HackerSchool/hswatch/Android/hswatch_connection_module/src/main/ic_launcher-playstore.png

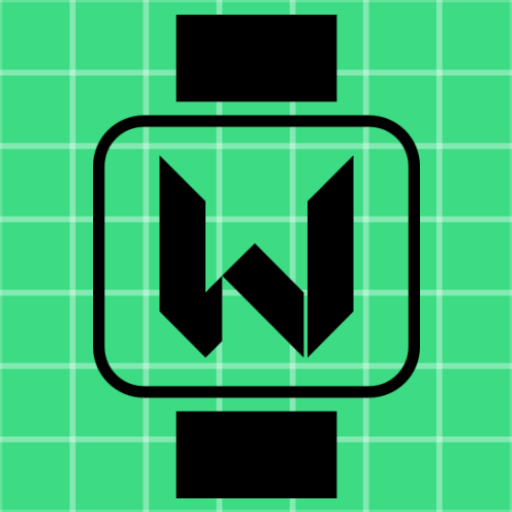
Android/hswatch_connection_module/src/main/ic_launcher-playstore.png
