HackerSchool/hswatch/docs/img/HSWatch_front.jpg

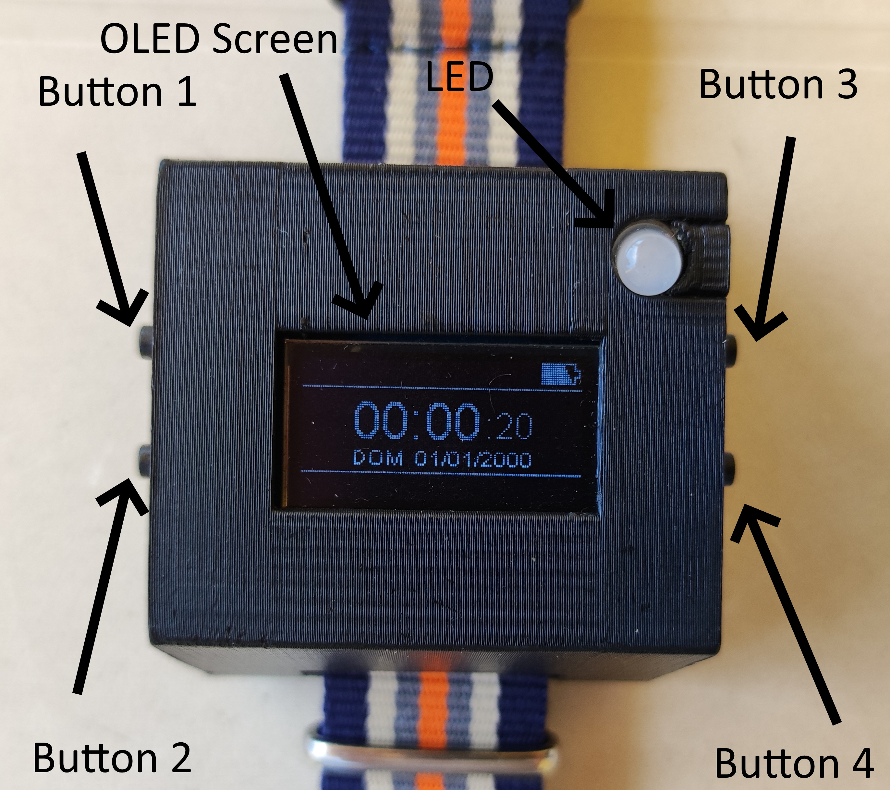
docs/img/HSWatch_front.jpg
