HackerSchool/hswatch/docs/img/HSWatch_side.jpg

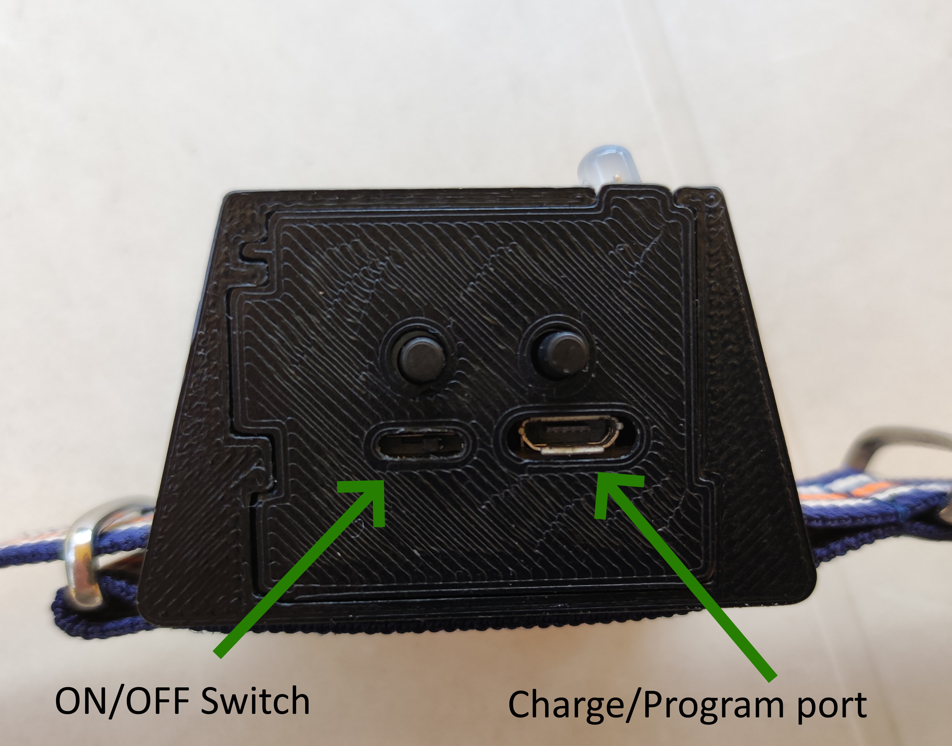
docs/img/HSWatch_side.jpg
