HackerSchool/hswatch/docs/img/pcb_back.png

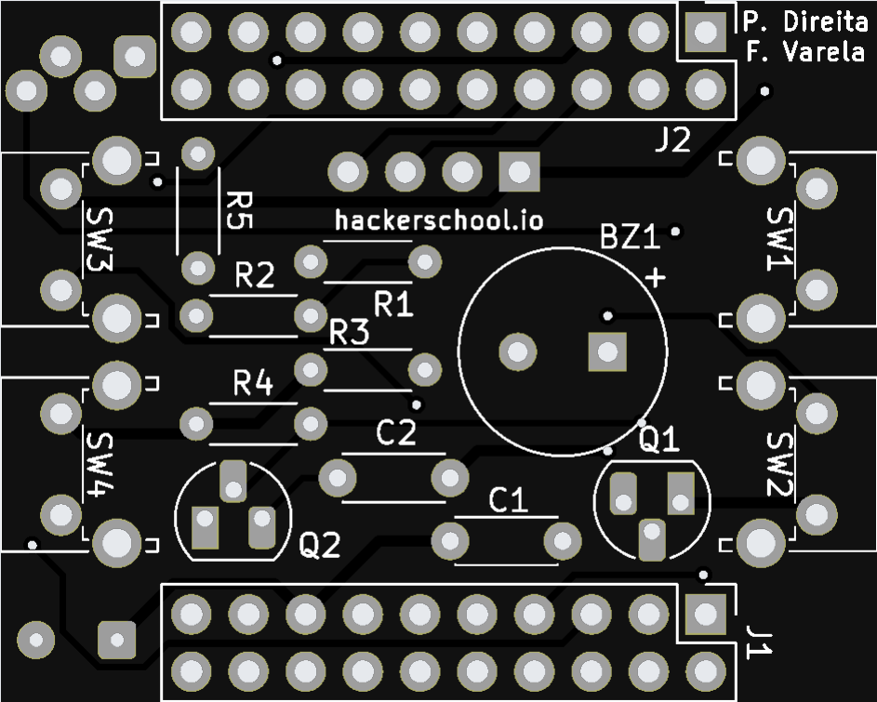
docs/img/pcb_back.png
