HackerSchool/hswatch/docs/img/pcb_front.png

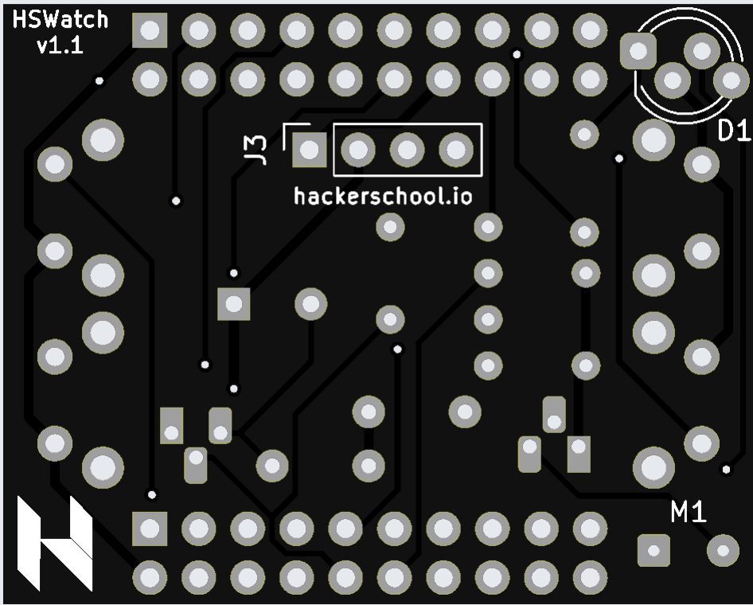
docs/img/pcb_front.png
