HackerSchool/hswatch/docs/img/peripheral_board_back.jpg

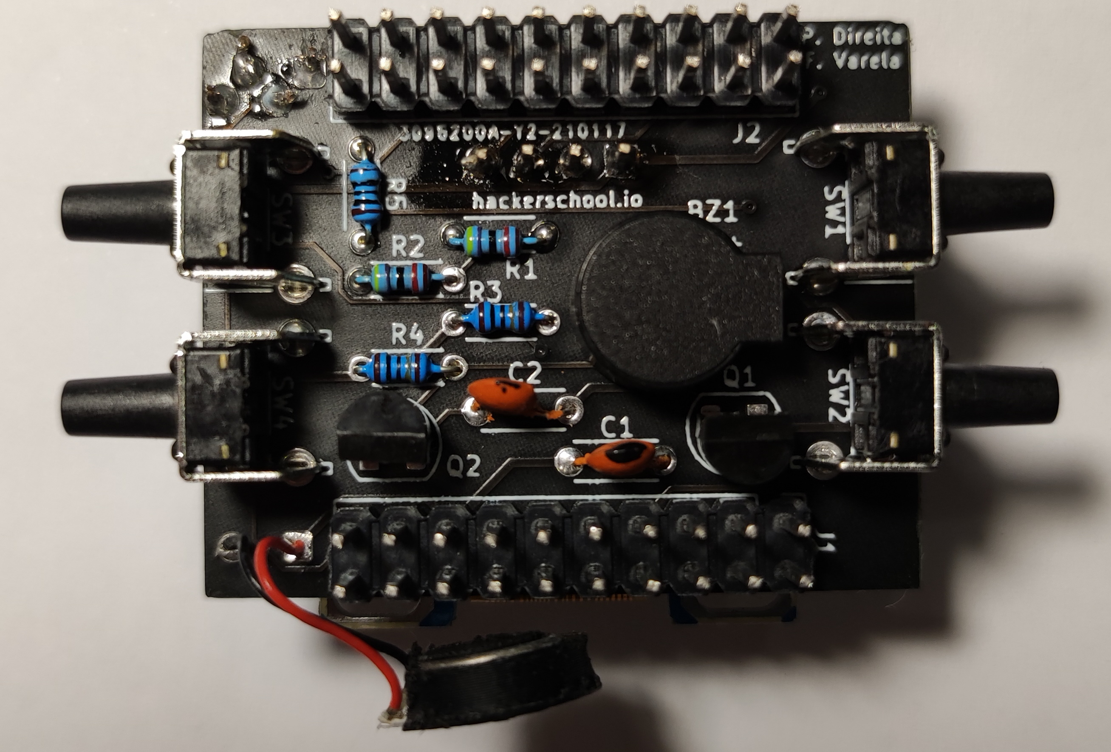
docs/img/peripheral_board_back.jpg
