HackerSchool/hswatch/docs/img/peripheral_board_front.jpg

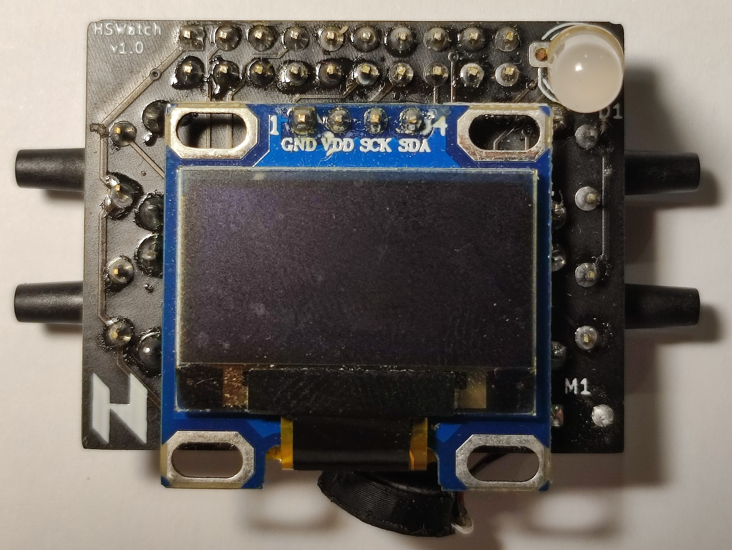
docs/img/peripheral_board_front.jpg
