HackerSchool/hswatch/docs/img/upload.png

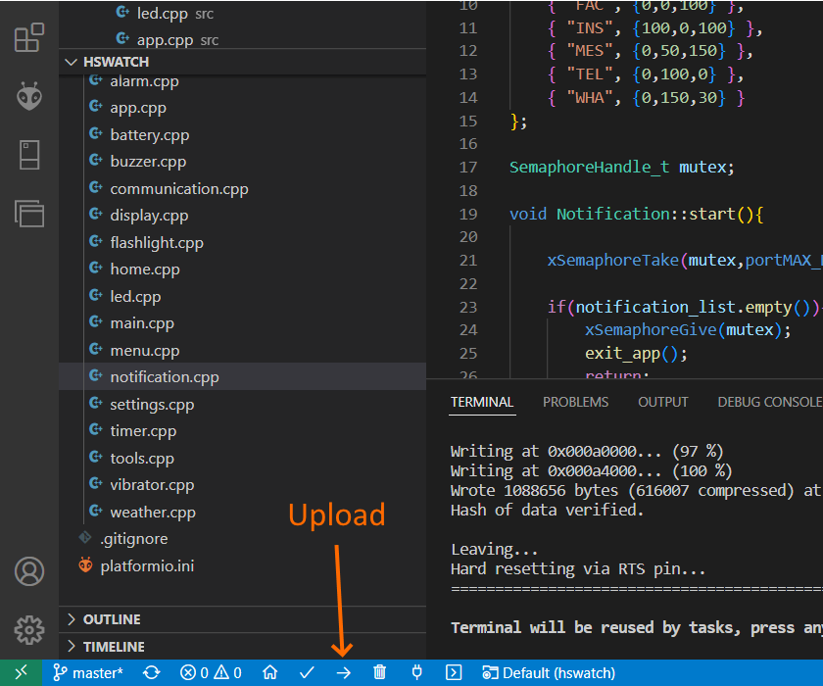
docs/img/upload.png
