HackerSchool/hswatch/docs/img/components/2N-700.jpg

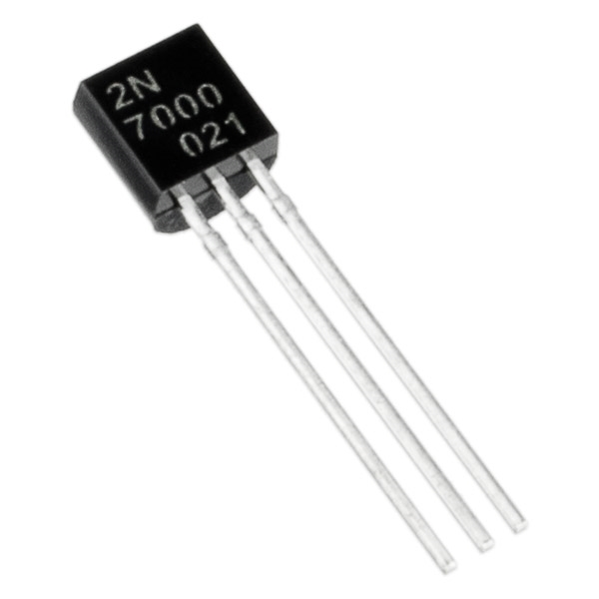
docs/img/components/2N-700.jpg
