HackerSchool/hswatch/docs/img/components/oled.png

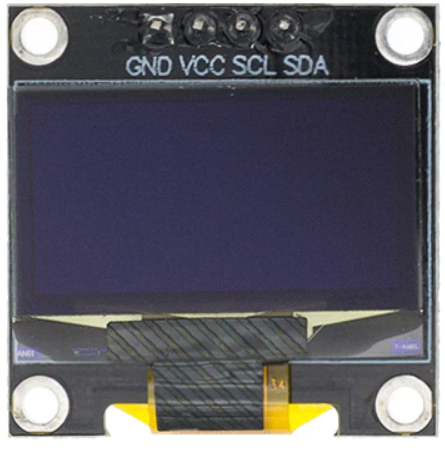
docs/img/components/oled.png
