HackerSchool/hswatch/docs/img/components/pin_header.jpg

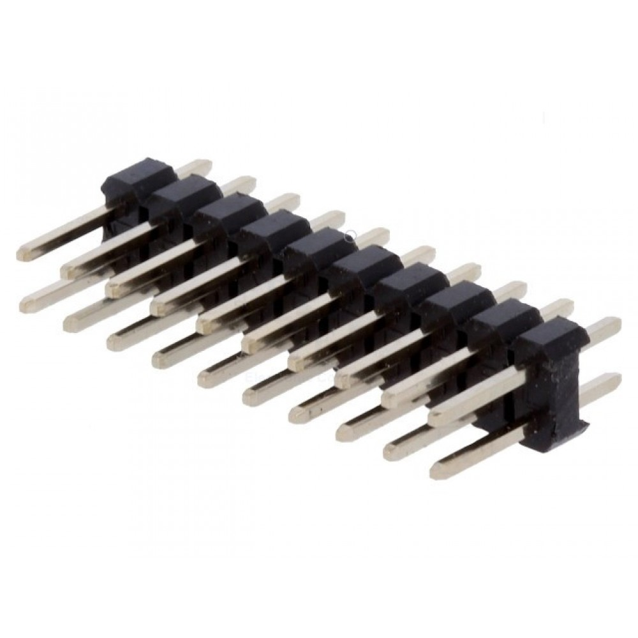
docs/img/components/pin_header.jpg
