HackerSchool/hswatch/docs/img/components/ttgo.png

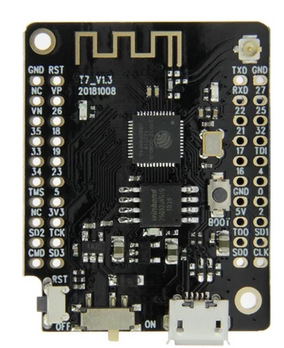
docs/img/components/ttgo.png
