HackerSchool/hswatch/docs/img/platformio-install.png

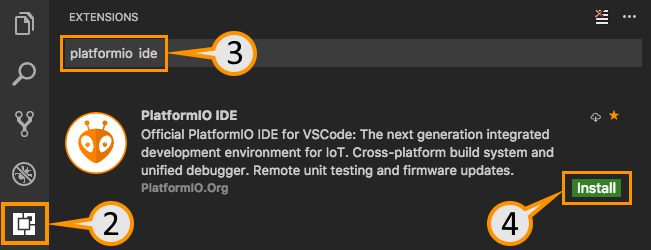
docs/img/platformio-install.png
