HackerSchool/hswatch/docs/img/soldering_tips.jpg

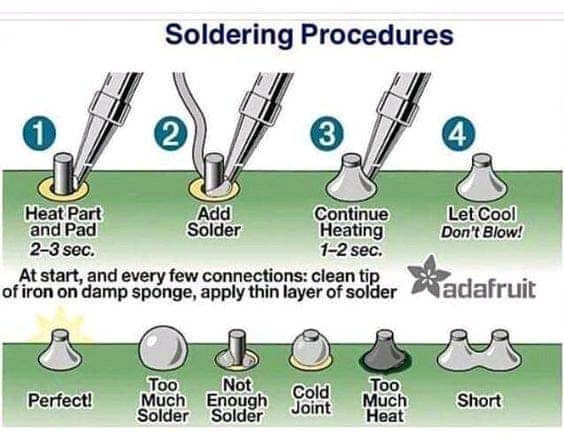
docs/img/soldering_tips.jpg
