HackerSchool/hswatch/docs/img/user_manual/alarm.png

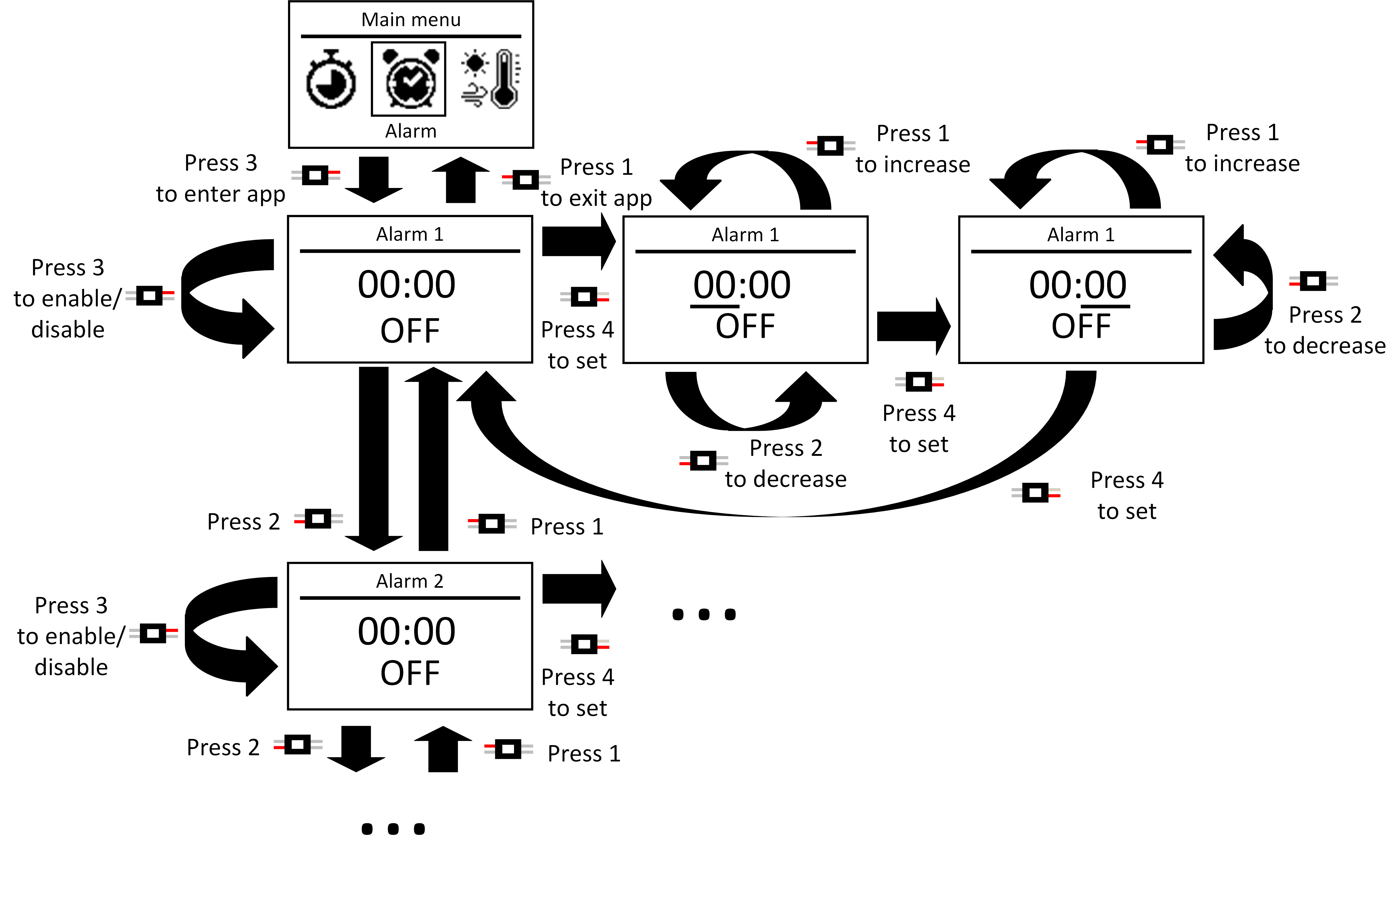
docs/img/user_manual/alarm.png
