HackerSchool/hswatch/docs/img/user_manual/chronograph_timer.png

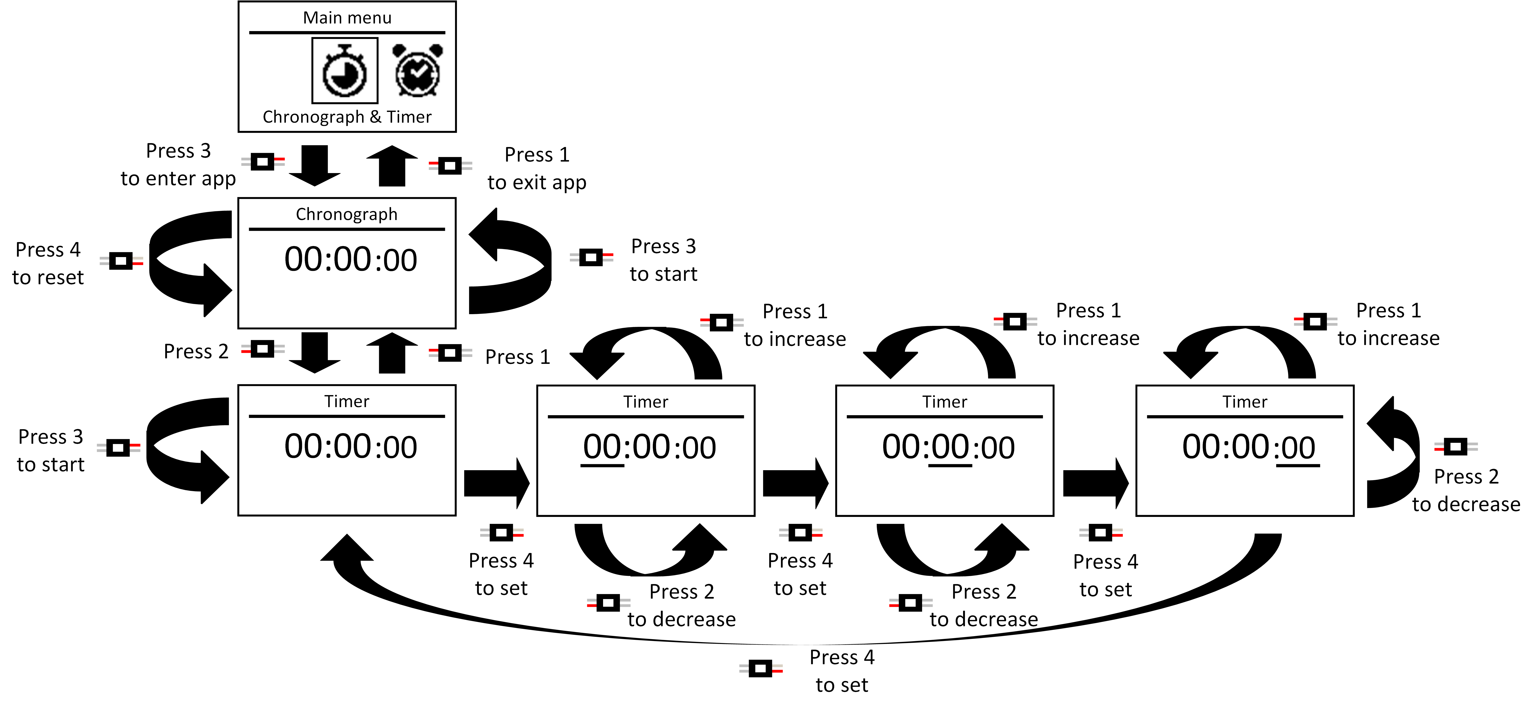
docs/img/user_manual/chronograph_timer.png
