HackerSchool/hswatch/docs/img/user_manual/clock_menu.png

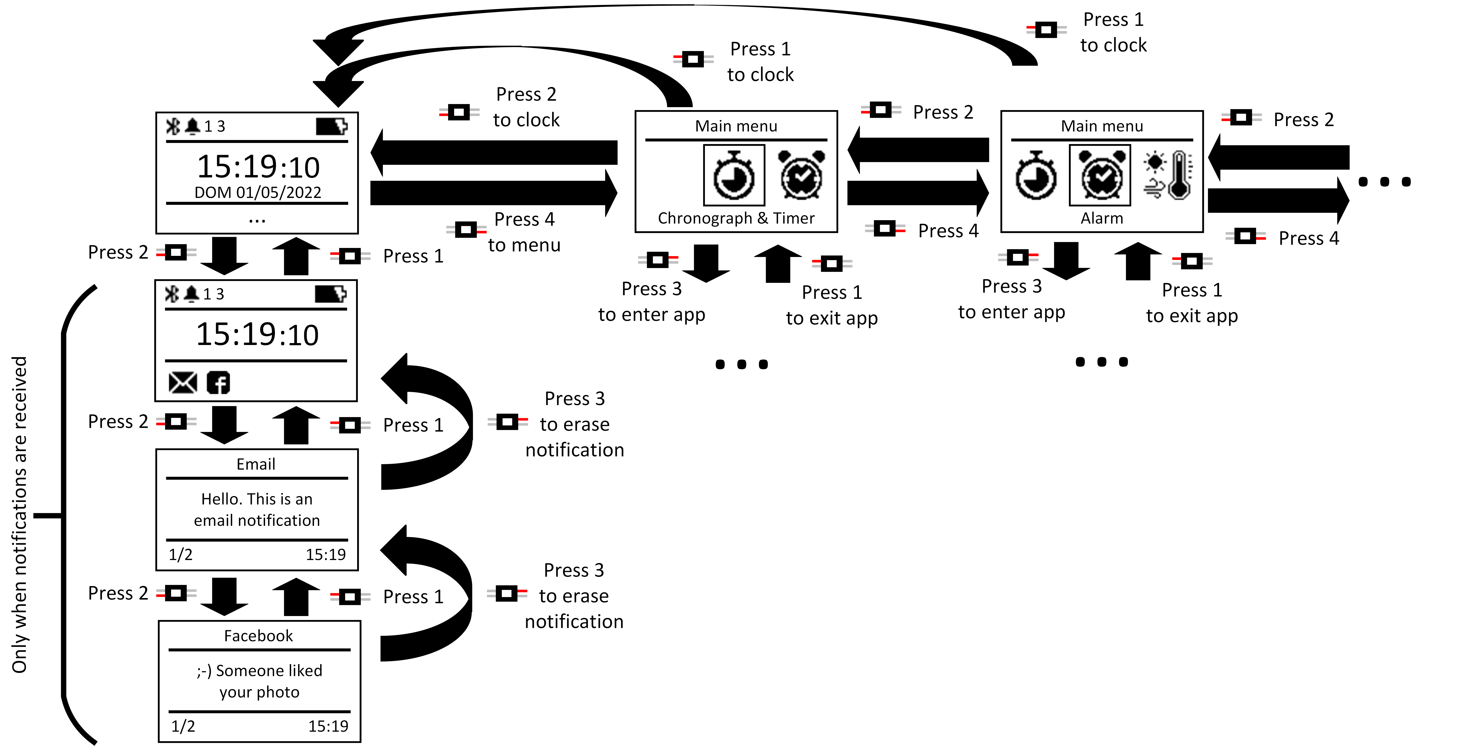
docs/img/user_manual/clock_menu.png
