HackerSchool/hswatch/docs/img/user_manual/flashlight.png

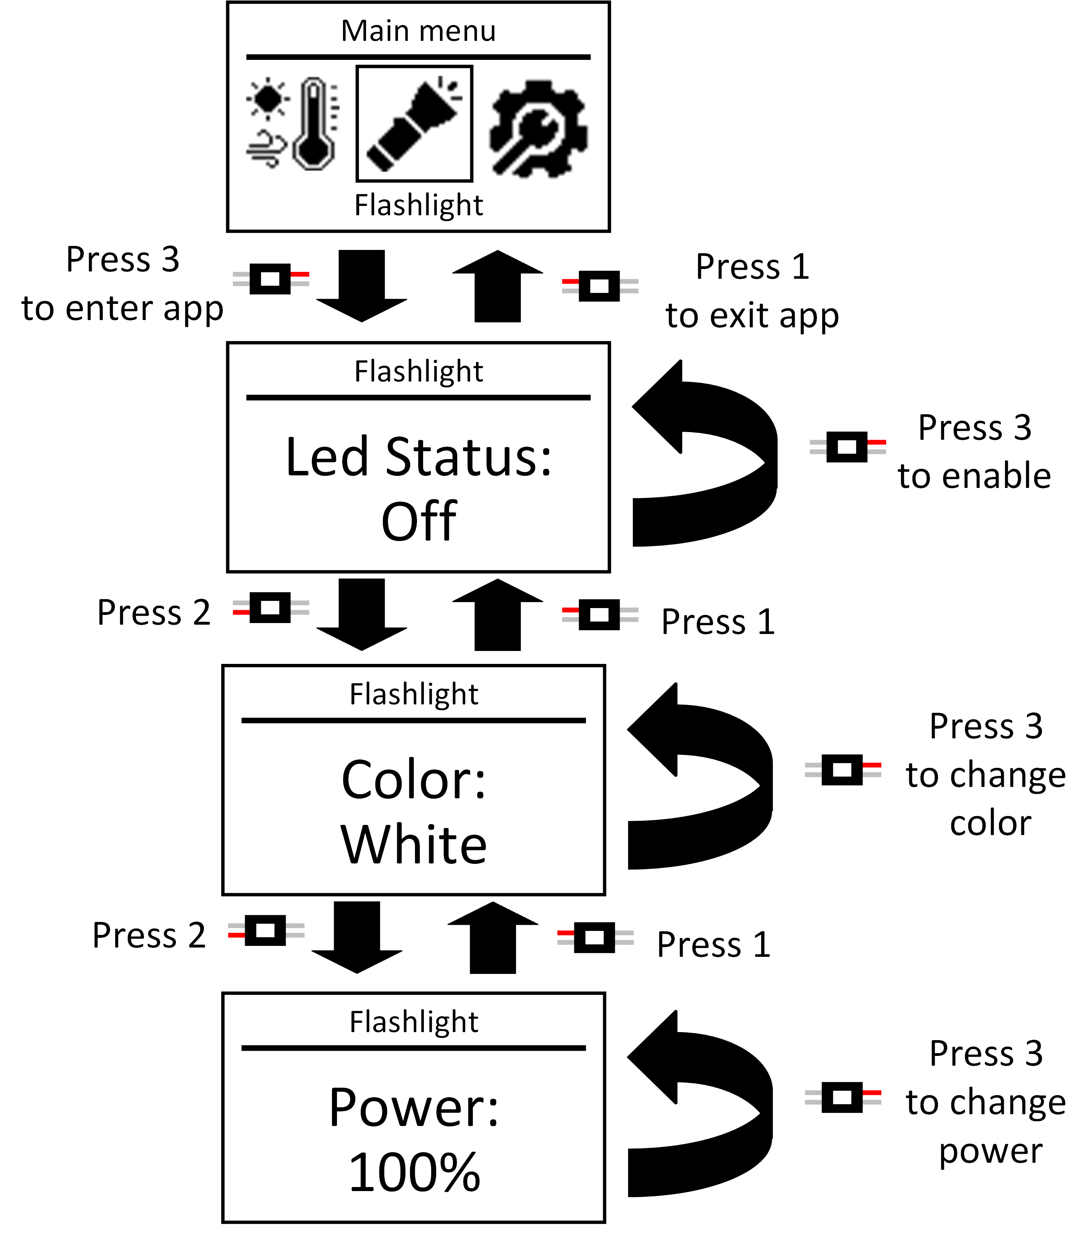
docs/img/user_manual/flashlight.png
