HackerSchool/hswatch/docs/img/user_manual/settings.png

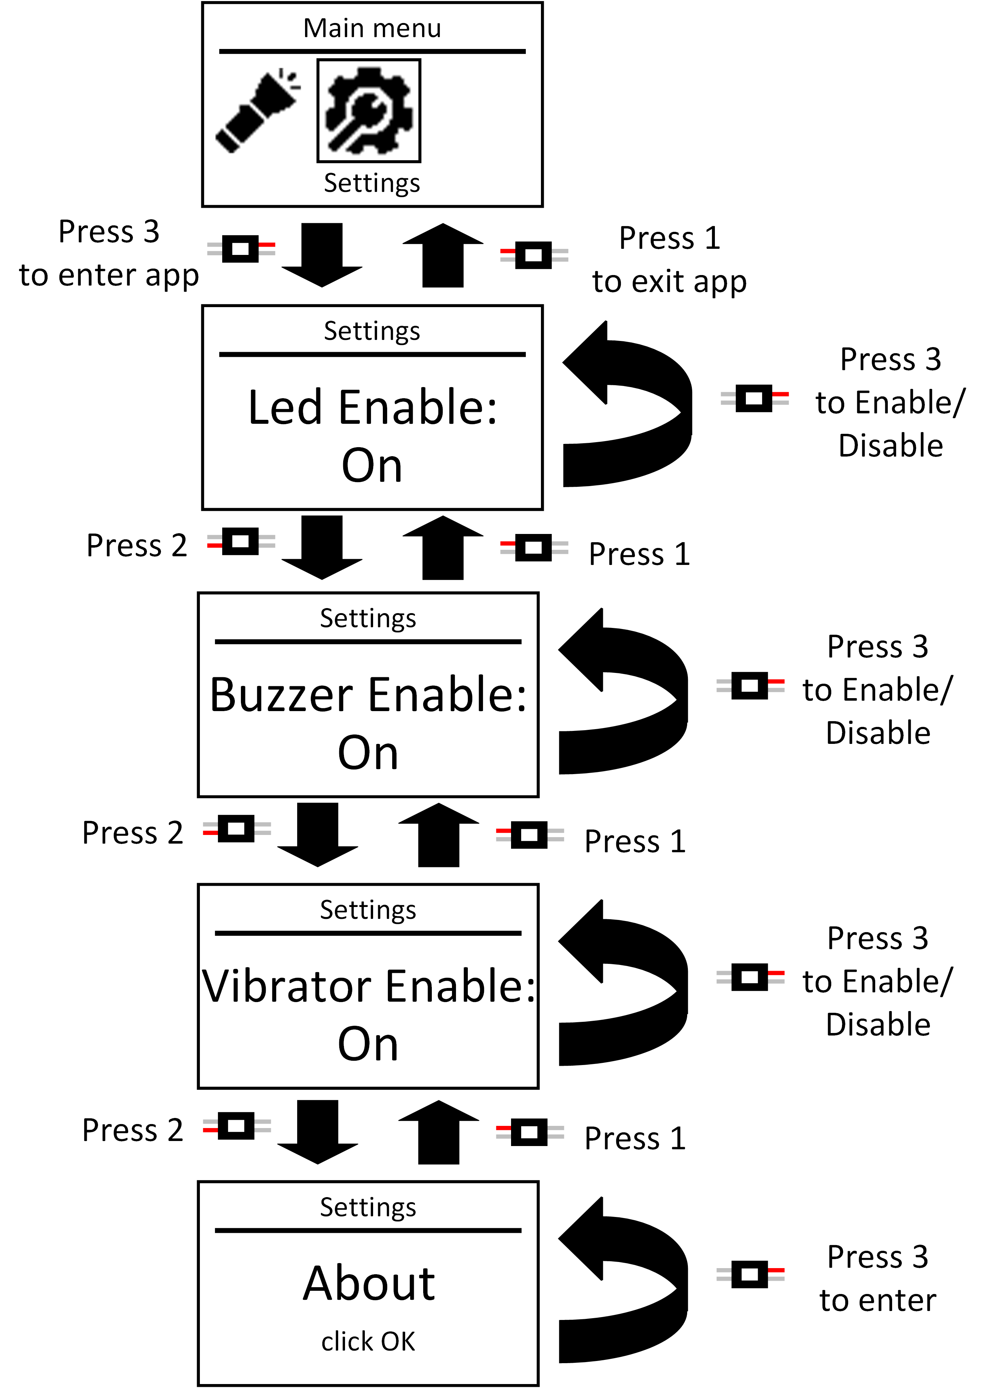
docs/img/user_manual/settings.png
