HackerSchool/hswatch/docs/img/user_manual/weather.png

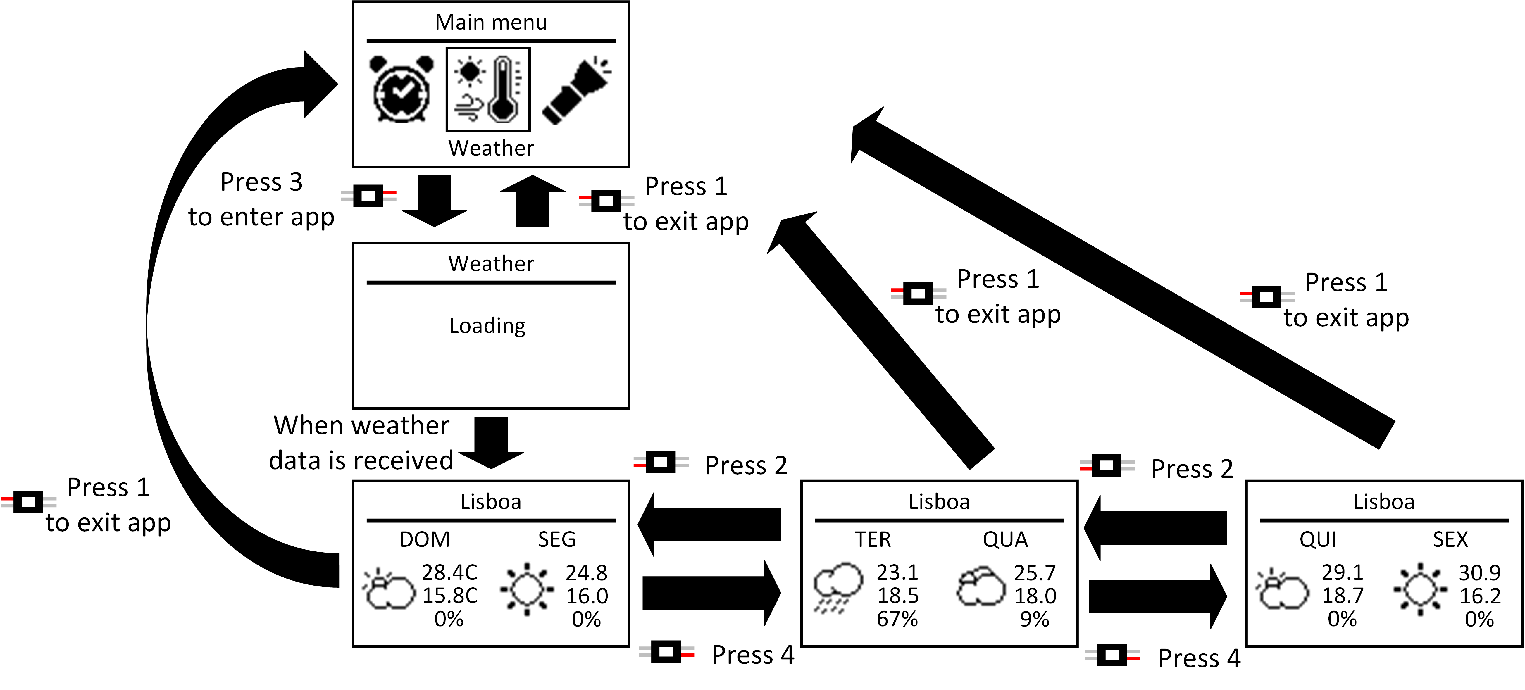
docs/img/user_manual/weather.png
