HackerSchool/hswatch/hswatch/include/logo_app.h

#define LOGO_APP_HEIGHT   32
#define LOGO_APP_WIDTH    32

static const unsigned char PROGMEM logo_alarm[] =
{ 0x78, 0x00, 0x00, 0x1E, 0xFC, 0x00, 0x00, 0x3F, 0xFE, 0x01, 0x80, 0x7F, 
  0xFE, 0x01, 0x80, 0x7F, 0xFE, 0x00, 0x00, 0x7F, 0x7E, 0xF0, 0x0F, 0x7E, 
  0x3C, 0xFC, 0x3F, 0x3C, 0x18, 0x1F, 0xF8, 0x18, 0x80, 0x03, 0xC0, 0x01, 
  0xC0, 0x31, 0x8C, 0x03, 0xE0, 0x7C, 0x3E, 0x07, 0x60, 0xFE, 0x7F, 0x06, 
  0x30, 0xFF, 0xEF, 0x0C, 0xB0, 0xFF, 0xC7, 0x1D, 0x98, 0xFF, 0xC3, 0x19, 
  0x98, 0xCF, 0xE1, 0x19, 0xD8, 0x8F, 0xF0, 0x1B, 0x08, 0x0F, 0xF8, 0x10, 
  0x08, 0x3F, 0xFC, 0x10, 0x08, 0x7F, 0xFE, 0x10, 0xD8, 0xFF, 0xFF, 0x1B, 
  0x98, 0xFF, 0xFF, 0x19, 0x98, 0xFF, 0xFF, 0x19, 0xB0, 0xFF, 0xFF, 0x0D, 
  0x30, 0xFF, 0xFF, 0x0C, 0x60, 0xFE, 0x7F, 0x06, 0xC0, 0x7C, 0x3E, 0x03, 
  0xC0, 0x31, 0x8C, 0x03, 0xC0, 0x03, 0xC0, 0x03, 0xE0, 0x0F, 0xF0, 0x07, 
  0x60, 0xFC, 0x3F, 0x06, 0x00, 0xE0, 0x07, 0x00 };

static const unsigned char PROGMEM logo_timer[] =
{ 0x00, 0xF0, 0x0F, 0x00, 0x00, 0xF0, 0x0F, 0x00, 0x00, 0xC0, 0x03, 0x00, 
  0x00, 0x80, 0x01, 0x00, 0x00, 0x80, 0x01, 0x00, 0x00, 0xC0, 0x03, 0x00, 
  0x40, 0xF8, 0x1F, 0x02, 0xE0, 0xFE, 0x7F, 0x07, 0xE0, 0x1F, 0xF8, 0x07, 
  0xC0, 0x07, 0xE0, 0x03, 0xC0, 0x01, 0x80, 0x03, 0xE0, 0x00, 0x07, 0x07, 
  0x70, 0x00, 0x1F, 0x0E, 0x70, 0x00, 0x3F, 0x0E, 0x38, 0x00, 0x7F, 0x1C, 
  0x38, 0x00, 0x7F, 0x1C, 0x18, 0x00, 0xFF, 0x18, 0x18, 0x00, 0xFF, 0x18, 
  0x18, 0x00, 0xFF, 0x18, 0x18, 0xFF, 0xFF, 0x18, 0x18, 0xFF, 0xFF, 0x18, 
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
  0x1E, 0x9F, 0xC1, 0x7F, 0x8C, 0x0F, 0xE0, 0x33, 0xC0, 0x07, 0xF8, 0x03, 
  0xE0, 0xE3, 0xFF, 0x01, 0xF0, 0xF1, 0xFF, 0x01, 0xF8, 0xF8, 0xFF, 0x01, 
  0x7C, 0xFC, 0xFF, 0x03, 0x3C, 0x3E, 0xFC, 0x03, 0x18, 0x3F, 0xF8, 0x00, 
  0x00, 0x1C, 0x38, 0x00, 0x00, 0x00, 0x00, 0x00, };
