HackerSchool/hswatch/hswatch/src/battery.cpp

#include "battery.h"

#define N_SAMPLES 5
#define SAMPLING_PERIOD 5
#define BATTERY_V_RANGE 515
#define FULL_LEVEL 2200
#define CHANGER 5

#define BATTERY_PIN 34

int level[N_SAMPLES] = {0};
int percentage = 100;
int status = 3;
int time_counter = 0;
int vector_iterator = 0; 
int changer=CHANGER;
int availble_samples=0;

void init_battery(){

}

void check_level_timer(){

	int l=0;
	int s;

	if(time_counter==0){

		if(availble_samples<N_SAMPLES){
			availble_samples++;
		}

		level[vector_iterator] = analogRead(BATTERY_PIN);

		for(int i=0; i<availble_samples;i++)
			l = l + level[i];

		l = l/availble_samples;

		//Serial.println(analogRead(BATTERY_PIN));
		
		percentage = (l-FULL_LEVEL+BATTERY_V_RANGE)*100/BATTERY_V_RANGE;

		//Serial.println(percentage);
		//Serial.println("--");

		if(percentage>100){
			percentage=100;
		}else if(percentage<0){
			percentage=0;
		}

		if(percentage>=70){
			s=3;
		}else if(percentage>=45){
			s=2;
		}else if(percentage>=20){
			s=1;
		}else{
			s=0;
		}

		if(s!=status){
			if(changer==CHANGER){
				status = s;
				changer = 0;
			}else{
				changer++;
			}
		}else{
			changer = 0;
		}

		if(vector_iterator<N_SAMPLES-1)
			vector_iterator++;
		else
			vector_iterator=0;
		
		time_counter = SAMPLING_PERIOD;
	}else{
		time_counter--;
	}
}

int percentage_battery(){
	return percentage;
}

int status_battery(){
	return status;
}
