HackerSchool/hswatch/hswatch/include/app.h

#ifndef APP_H
#define APP_H

#include <Arduino.h>
#include <list>

//typedef struct AppListHandler app_list_handler;

class App {

	public:

		const String id;
		const String name;
		const unsigned char* logo;

		virtual void start() =0;
		virtual void display();
		virtual void but_up_left();
		virtual void but_up_right();
		virtual void but_down_left();
		virtual void but_down_right();
		virtual void bt_receive(char*);
		virtual void timer_1s();
		virtual void exit();

		App(String,String,const unsigned char*);

		static void exit_app();
		static void run_app(String);
		static App* curr_app();

		static App* app_search_by_name(String);
		static App* app_search_by_id(String);
		static std::list<App*> app_list_show();

		void attach_timer();
		void detach_timer();
		static void call_timer();

		static void init_app();

	private:

		static std::list<App*> app_stack;
		static std::list<App*> app_list;
		static std::list<App*> timer_attached_app;

		static void detach_timer_task(void*);
};

#endif
