HackerSchool/hswatch/hswatch/include/logo_hs.h

#define LOGO_HEIGHT   64
#define LOGO_WIDTH    56

static const unsigned char PROGMEM logo_hs[] =
{ 0x00, 0x00, 0x00, 0x00, 0x00, 0x00, 0x00, 0x00, 0x00, 0x00, 0x00, 0x00, 
	0x00, 0x00, 0x10, 0x00, 0x00, 0x00, 0x10, 0x00, 0x00, 0x30, 0x00, 0x00, 
	0x00, 0x30, 0x00, 0x00, 0x70, 0x00, 0x00, 0x00, 0x70, 0x00, 0x00, 0xF0, 
	0x00, 0x00, 0x00, 0xF0, 0x00, 0x00, 0xF0, 0x01, 0x00, 0x00, 0xF0, 0x01, 
	0x00, 0xF0, 0x03, 0x00, 0x00, 0xF0, 0x03, 0x00, 0xF0, 0x07, 0x00, 0x00, 
	0xF0, 0x07, 0x00, 0xF0, 0x0F, 0x00, 0x00, 0xF0, 0x0F, 0x00, 0xF0, 0x1F, 
	0x00, 0x00, 0xF0, 0x1F, 0x00, 0xF0, 0x3F, 0x00, 0x00, 0xF0, 0x3F, 0x00, 
	0xF0, 0x7F, 0x00, 0x00, 0xF0, 0x7F, 0x00, 0xF0, 0xFF, 0x00, 0x00, 0xF0, 
	0xFF, 0x00, 0xF0, 0xFF, 0x01, 0x00, 0xF0, 0xFF, 0x01, 0xF0, 0xFF, 0x01, 
	0x00, 0xF0, 0xFF, 0x01, 0xF0, 0xFF, 0x01, 0x00, 0xF0, 0xFF, 0x01, 0xF0, 
	0xFF, 0x01, 0x00, 0xF0, 0xFF, 0x01, 0xF0, 0xFF, 0x01, 0x00, 0xF0, 0xFF, 
	0x01, 0xF0, 0xFF, 0x01, 0x00, 0xF0, 0xFF, 0x01, 0xF0, 0xFF, 0x01, 0x00, 
	0xF0, 0xFF, 0x01, 0xF0, 0xFF, 0x01, 0x00, 0xF0, 0xFF, 0x01, 0xF0, 0xFF, 
	0x01, 0x00, 0xF0, 0xFF, 0x01, 0xF0, 0xFF, 0x01, 0x00, 0xF0, 0xFF, 0x01, 
	0xF0, 0xFF, 0x01, 0x00, 0xF0, 0xFF, 0x01, 0xF0, 0xFF, 0x01, 0x00, 0xF0, 
	0xFF, 0x01, 0xF0, 0xFF, 0x01, 0x00, 0xF0, 0xFF, 0x01, 0xF0, 0xFF, 0x01, 
	0x00, 0xE0, 0xFF, 0x01, 0xF0, 0xFF, 0xFF, 0xFF, 0xCF, 0xFF, 0x01, 0xF0, 
	0xFF, 0xFD, 0xFF, 0x9F, 0xFF, 0x01, 0xF0, 0xFF, 0xF9, 0xFF, 0x3F, 0xFF, 
	0x01, 0xF0, 0xFF, 0xF1, 0xFF, 0x7F, 0xFE, 0x01, 0xF0, 0xFF, 0xE1, 0xFF, 
	0xFF, 0xFC, 0x01, 0xF0, 0xFF, 0xC1, 0xFF, 0xFF, 0xF9, 0x01, 0xF0, 0xFF, 
	0x81, 0xFF, 0xFF, 0xF3, 0x01, 0xF0, 0xFF, 0x01, 0xFF, 0xFF, 0xE7, 0x01, 
	0xF0, 0xFF, 0x01, 0xFE, 0xFF, 0xCF, 0x01, 0xF0, 0xFF, 0x01, 0xFC, 0xFF, 
	0x9F, 0x01, 0xF0, 0xFF, 0x01, 0xF8, 0xFF, 0x3F, 0x01, 0xF0, 0xFF, 0x01, 
	0xF0, 0xFF, 0x7F, 0x00, 0xF0, 0xFF, 0x01, 0xE0, 0xFF, 0xFF, 0x00, 0xF0, 
	0xFF, 0x01, 0xC0, 0xFF, 0xFF, 0x01, 0xF0, 0xFF, 0x01, 0x80, 0xFF, 0xFF, 
	0x01, 0xF0, 0xFF, 0x01, 0x00, 0xFF, 0xFF, 0x01, 0xF0, 0xFF, 0x01, 0x00, 
	0xFE, 0xFF, 0x01, 0xF0, 0xFF, 0x01, 0x00, 0xFC, 0xFF, 0x01, 0xF0, 0xFF, 
	0x01, 0x00, 0xF8, 0xFF, 0x01, 0xE0, 0xFF, 0x01, 0x00, 0xF0, 0xFF, 0x01, 
	0xC0, 0xFF, 0x01, 0x00, 0xE0, 0xFF, 0x01, 0x80, 0xFF, 0x01, 0x00, 0xC0, 
	0xFF, 0x01, 0x00, 0xFF, 0x01, 0x00, 0x80, 0xFF, 0x01, 0x00, 0xFE, 0x01, 
	0x00, 0x00, 0xFF, 0x01, 0x00, 0xFC, 0x01, 0x00, 0x00, 0xFE, 0x01, 0x00, 
	0xF8, 0x01, 0x00, 0x00, 0xFC, 0x01, 0x00, 0xF0, 0x01, 0x00, 0x00, 0xF8, 
	0x01, 0x00, 0xE0, 0x01, 0x00, 0x00, 0xF0, 0x01, 0x00, 0xC0, 0x01, 0x00, 
	0x00, 0xE0, 0x01, 0x00, 0x80, 0x01, 0x00, 0x00, 0xC0, 0x01, 0x00, 0x00, 
	0x01, 0x00, 0x00, 0x80, 0x01, 0x00, 0x00, 0x00, 0x00, 0x00, 0x00, 0x01, 
	0x00, 0x00, 0x00, 0x00, 0x00, 0x00, 0x00, 0x00, 0x00, 0x00, 0x00, 0x00, 
	0x00, 0x00, 0x00, 0x00, 0x00, 0x00, 0x00, 0x00, 0x00, 0x00, 0x00, 0x00, 
	0x00, 0x00, 0x00, 0x00 };
